fixxl/el-fueradoro/Manual/Bilder/rfm-dil-70x100.pdf

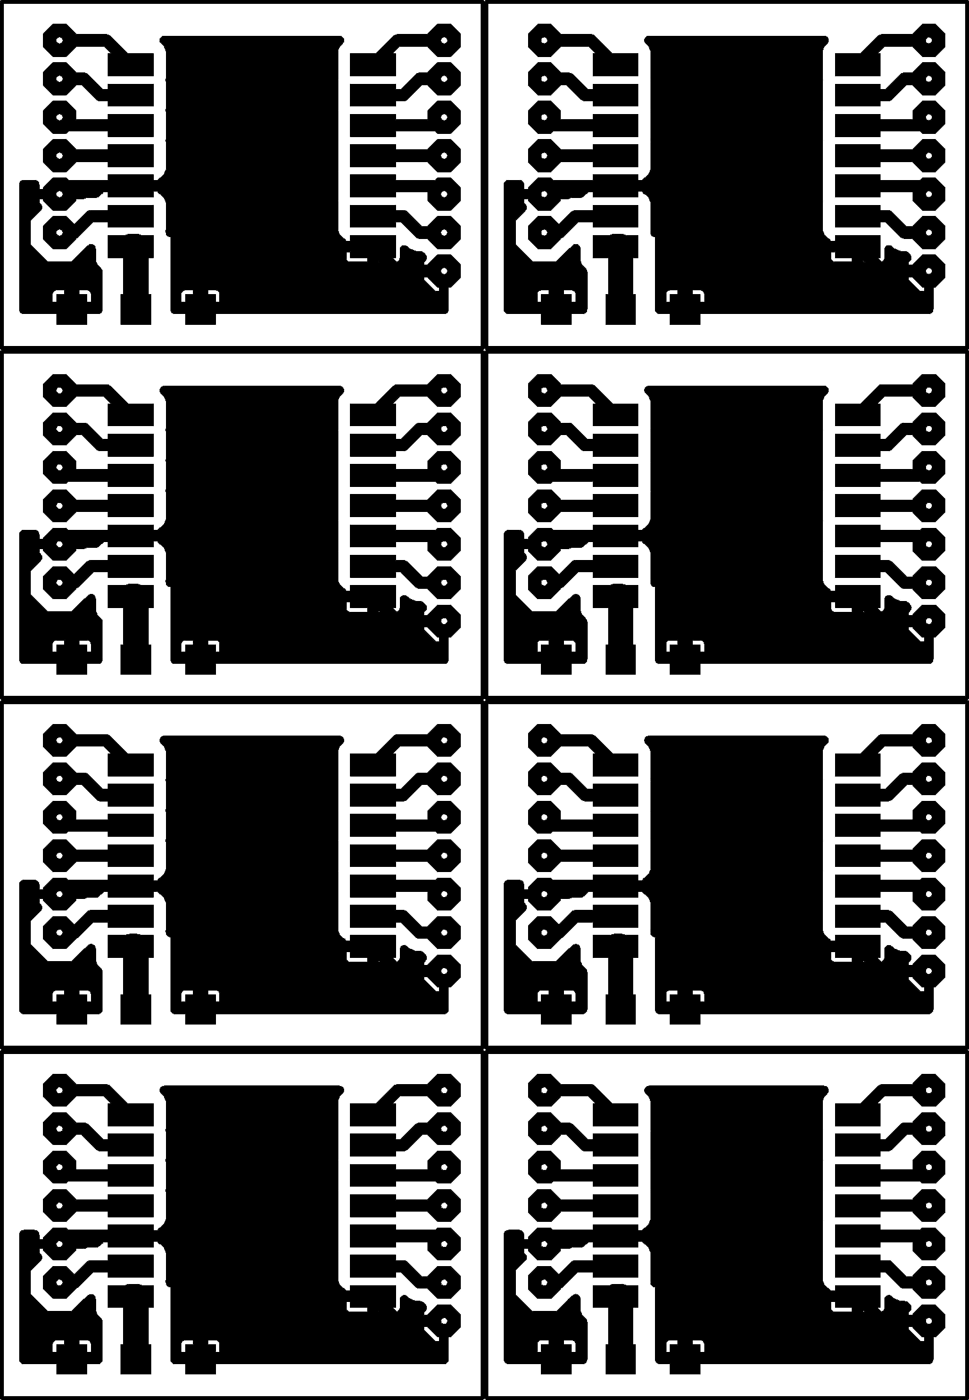
[picture p66: page 1]
