fixxl/el-fueradoro/Manual/Bilder/Transmitterschaltplan.pdf

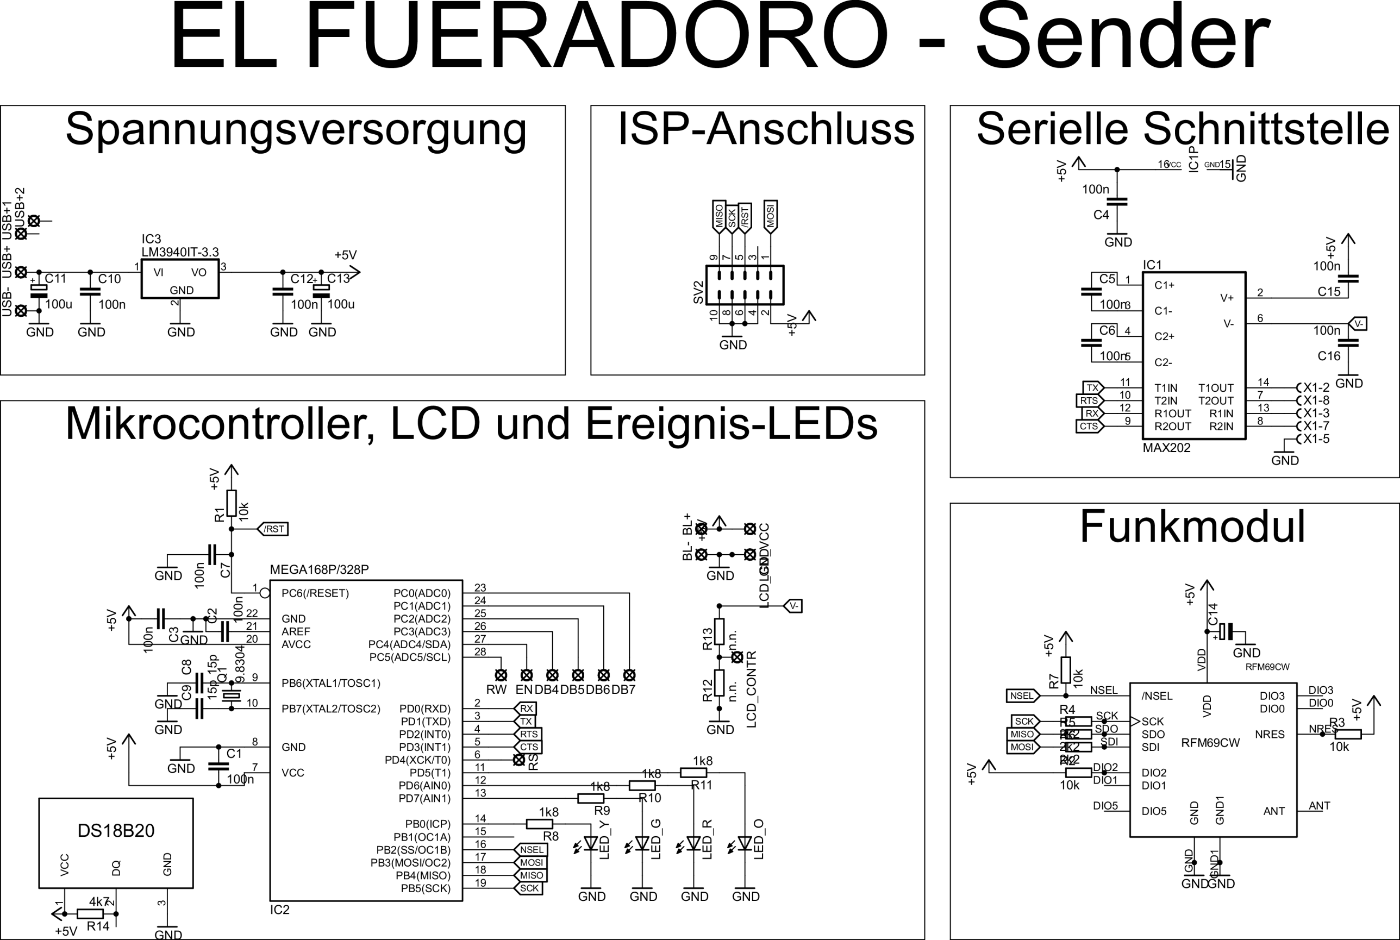
[picture p67: page 1]
