fixxl/el-fueradoro/Manual/Bilder/german.jpg

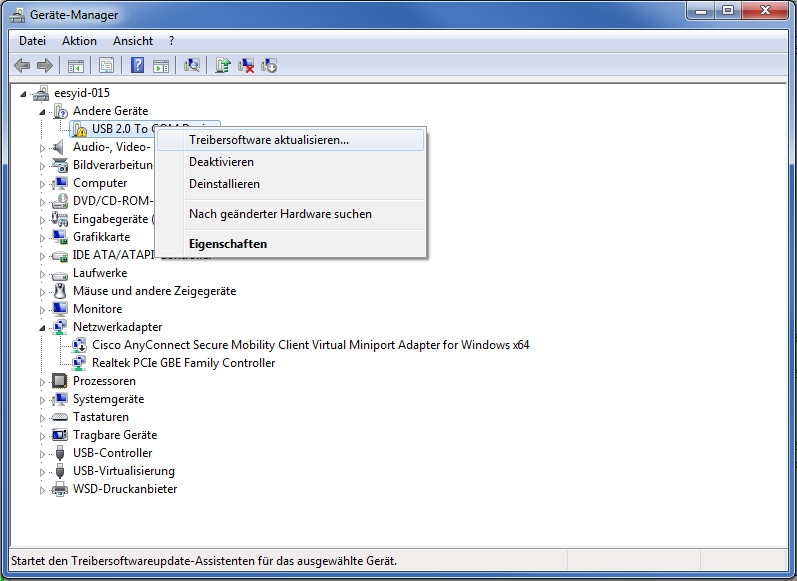
Manual/Bilder/german.jpg
