fixxl/el-fueradoro/Manual/Bilder/platine_v2.jpg

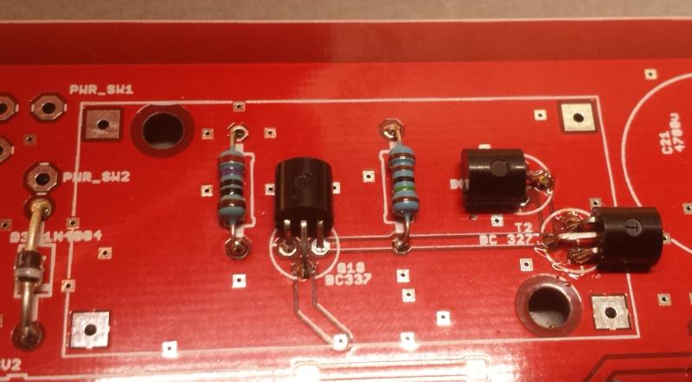
Manual/Bilder/platine_v2.jpg
