fixxl/el-fueradoro/Manual/Bilder/SenderMitAdapter.jpg

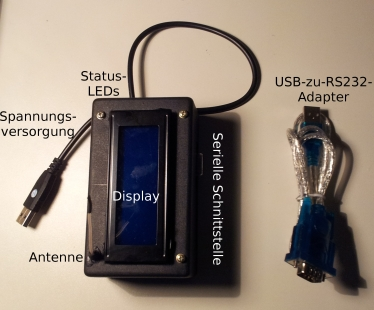
Manual/Bilder/SenderMitAdapter.jpg
