fixxl/el-fueradoro/Manual/Bilder/treiber.jpg

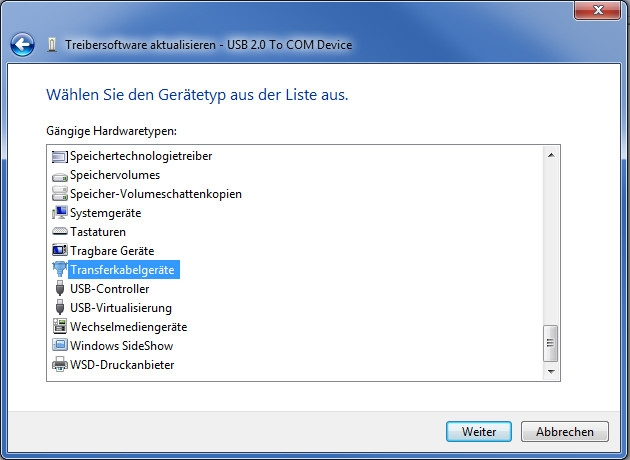
Manual/Bilder/treiber.jpg
