fixxl/el-fueradoro/Manual/Bilder/Zuendboxschaltplan.pdf

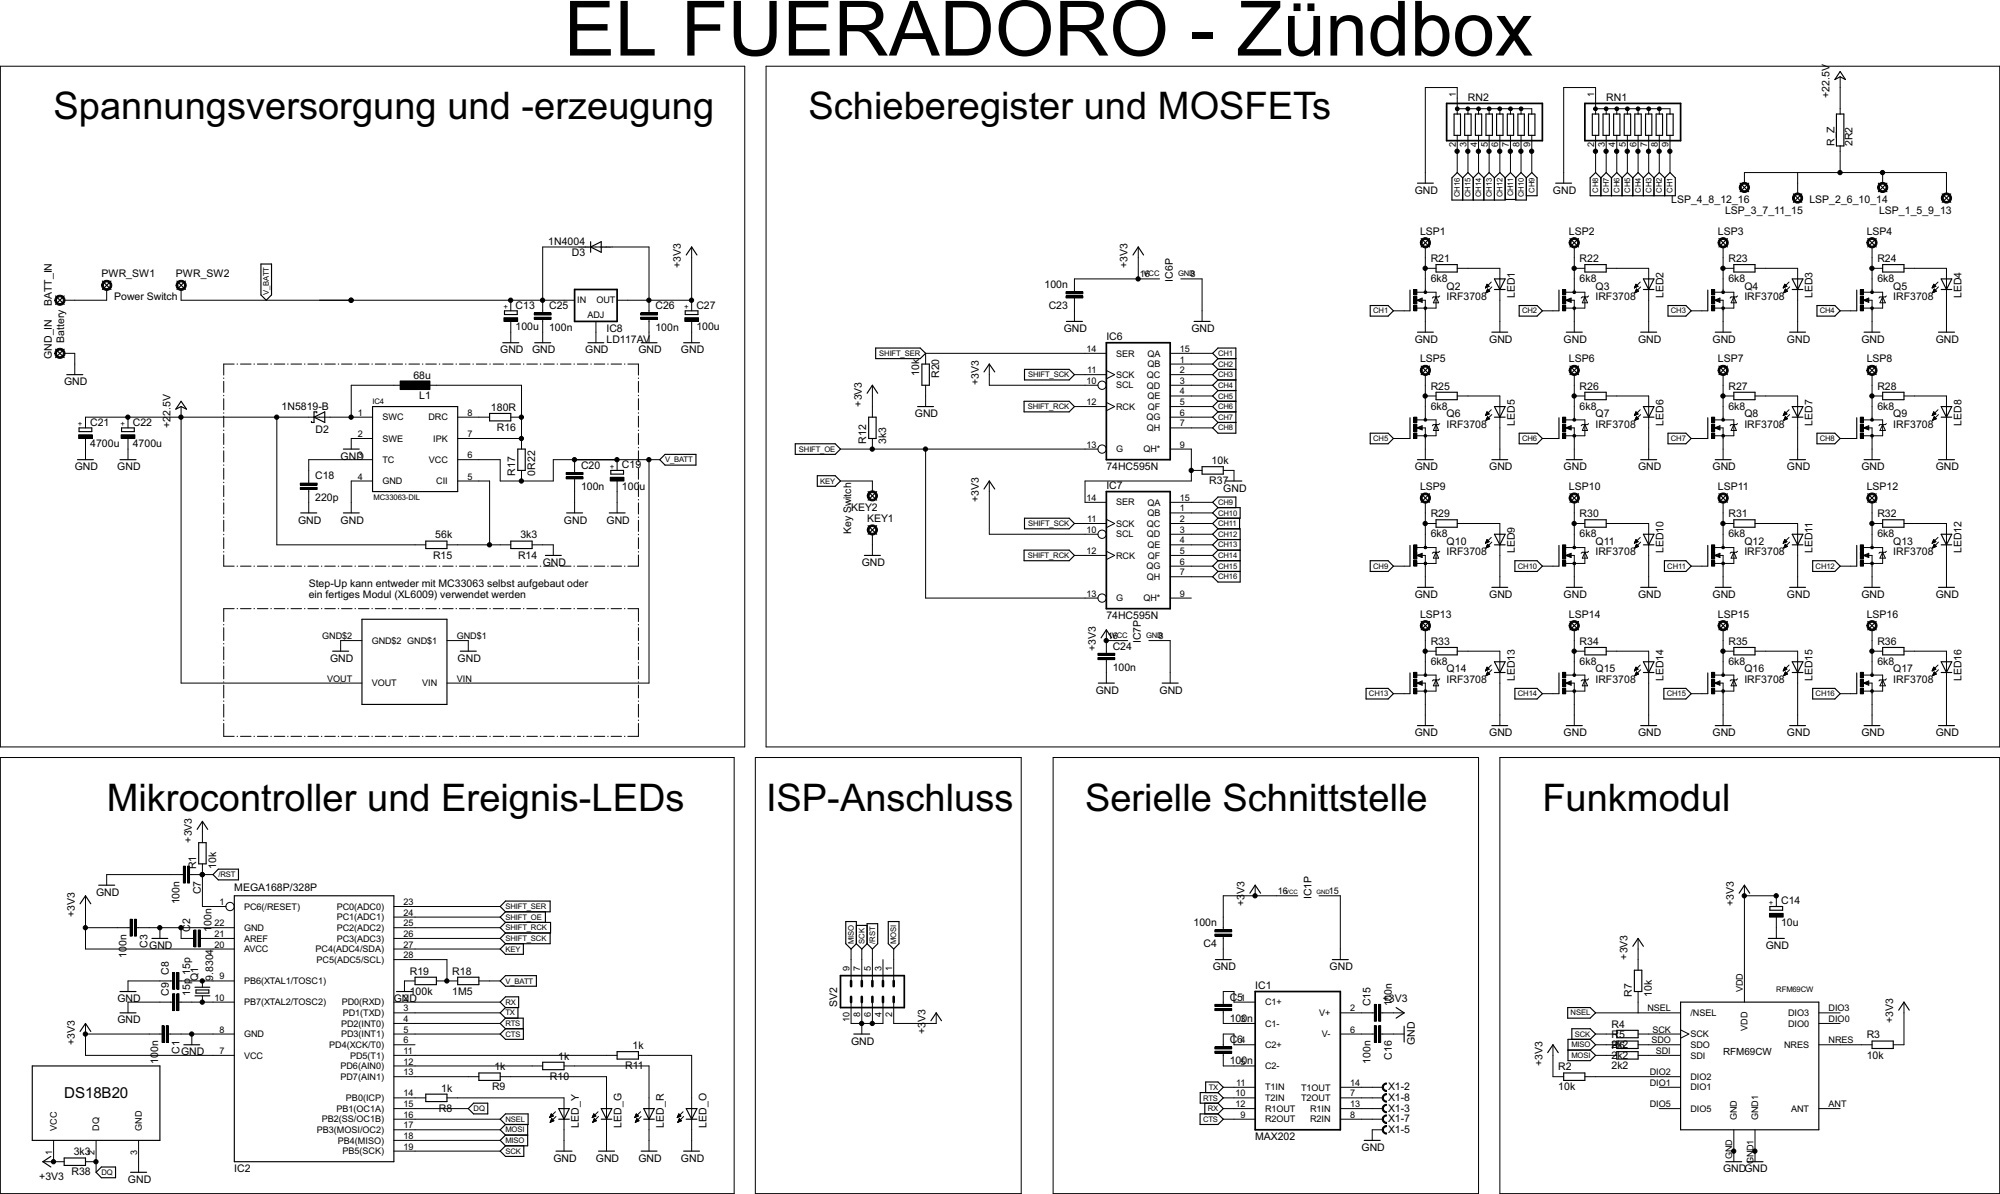
[picture p73: page 1]

Step-Up kann entweder mit MC33063 selbst aufgebaut oder
ein fertiges Modul (XL6009) verwendet werden

GND | AREF 21 AVCC 20 | SHIFT_RCK SHIFT_SCK

PB6(XTAL1/TOSC1) 9 | KEY
