fixxl/el-fueradoro/Manual/Bilder/Zuendboxbottom.pdf

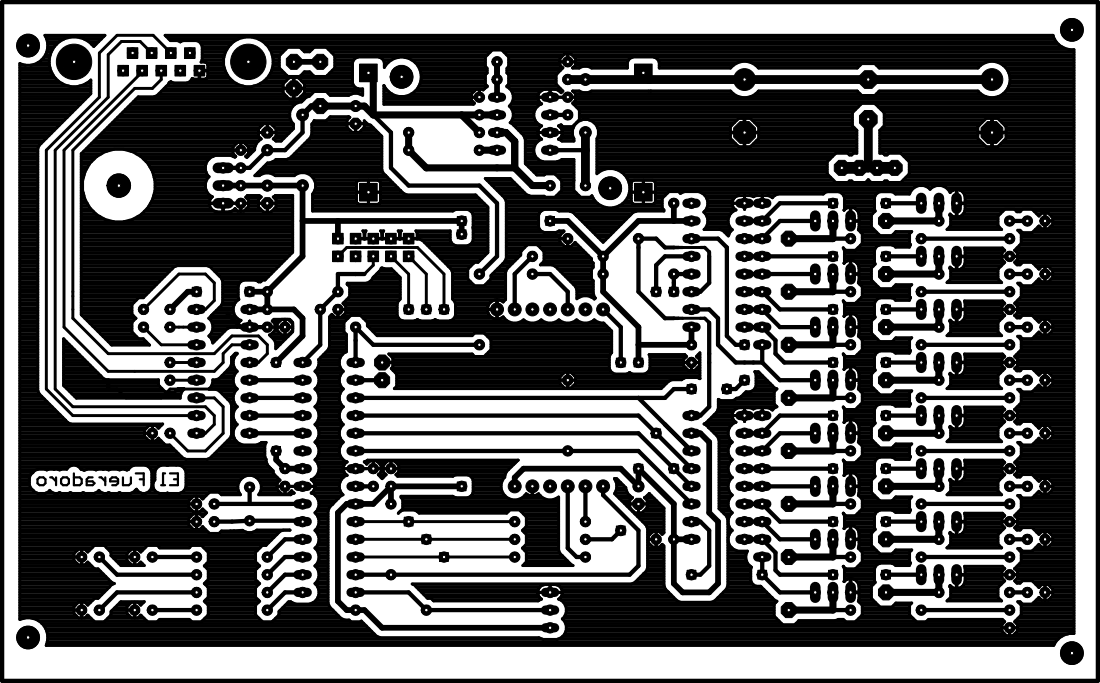
[picture p83: page 1]
