fixxl/el-fueradoro/Manual/Bilder/Zuendboxtop.pdf

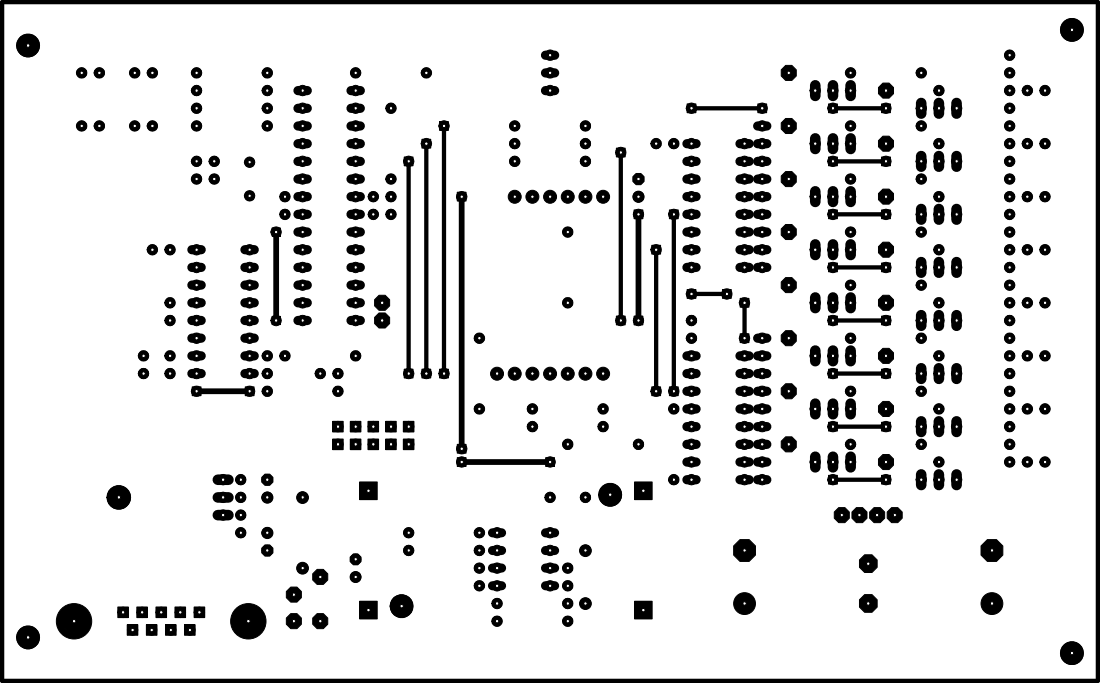
[picture p84: page 1]
