fixxl/el-fueradoro/Hexfiles/Updater/UpdateLoader.ini

[UpdateLoader]
ComPort=2
BootloaderPassword=Peda
FirmwareFilename=Pyro_v3_atmega328p_RFM69_HP.hex
Page=2

[Advanced]
BaudRate=9600
FirmwareKeyParseMode=1
ShowMemory=0
HideMessages=1
Enabled=1
ProgramWrite=1
ProgramVerify=1
ProgramStart=1
ReloadFile=1
DetectOneWire=0
ToggleDTR=0
InvertCom=0
EnableFirmwareKey=1
FirmwareKeyOnce=1
FirmwareKey=0A 6B 69 6C 6C 0A
ConnectTries=250

[PaketMode]
Enabled=1
MiniGUI=0
ModalGUI=0
HideAdvancedMode=1
LockFilename=0
LockPassword=1
HidePassword=1
