fixxl/el-fueradoro/Firmware_Minimodul/rfm69.h

/*
 * rfm69.h
 *
 * Definitionen und Funktionen zur Steuerung des Funkmoduls RFM69
 *
 */

#ifndef RFM69_H_
#define RFM69_H_

/* Carrierfrequenz in Hz */
#ifndef FREQUENCY
    #define FREQUENCY              869500000LL
#endif

/* Bitrate in bps (1200 ... 300000) and shall it be calculated as for RFM12
 * in order to get equal bitrate for RFM12 and RFM69 if used together? */
#define BITRATE                9600L
#define RFM12COMP              1

/* Minimum PA ramp up time in microseconds to set in register 0x12.
 * If value is not defined in table, next higher value will be chosen */
#define RFM_RAMP_UP            40

/* Output power in dBm (-18...13) */
#ifndef P_OUT_DBM
    #define P_OUT_DBM          10 // Output power in dBm
#endif

#ifndef HPVERSION
    #define HPVERSION          0
#endif

#ifndef SQUELCH_THRESHOLD
    #define SQUELCH_UPPER_LIMIT  -70
#endif

#ifndef RX_TIMEOUT_CTR_THRESHOLD_HIGH
    #define RX_TIMEOUT_CTR_THRESHOLD_HIGH 20
#endif

#ifndef RX_TIMEOUT_CTR_THRESHOLD_TP
    #define RX_TIMEOUT_CTR_THRESHOLD_TP 6
#endif

#ifndef RX_TIMEOUT_CTR_THRESHOLD_LOW
    #define RX_TIMEOUT_CTR_THRESHOLD_LOW 2
#endif
/* Pin assignment */
#define NSELPORT               C
#define NSEL                   3
#define SDIPORT                B
#define SDI                    3
#define SDOPORT                B
#define SDO                    4
#define SCKPORT                B
#define SCK                    5

/* Use Hardware-SPI if available? */
#define RFM69_USE_HARDWARE_SPI 1

// Don't change anything from here
#define XTALFREQ               32000000UL

#define NSEL_PORT              PORT( NSELPORT )
#define NSEL_DDR               DDR( NSELPORT )
#define NSEL_PIN               PIN( NSELPORT )
#define NSEL_NUMERIC           NUMPORT( NSELPORT )

#define SDI_PORT               PORT( SDIPORT )
#define SDI_DDR                DDR( SDIPORT )
#define SDI_PIN                PIN( SDIPORT )
#define SDI_NUMERIC            NUMPORT( SDIPORT )

#define SDO_PORT               PORT( SDOPORT )
#define SDO_DDR                DDR( SDOPORT )
#define SDO_PIN                PIN( SDOPORT )
#define SDO_NUMERIC            NUMPORT( SDOPORT )

#define SCK_PORT               PORT( SCKPORT )
#define SCK_DDR                DDR( SCKPORT )
#define SCK_PIN                PIN( SCKPORT )
#define SCK_NUMERIC            NUMPORT( SCKPORT )

#define ACTIVATE_RFM           NSEL_PORT &= ~( 1 << NSEL )
#define DEACTIVATE_RFM         NSEL_PORT |= ( 1 << NSEL )


#define FRF                    ( ( FREQUENCY * 524288LL + ( XTALFREQ / 2 ) ) / XTALFREQ )
#define FRF_MSB                ( ( FRF >> 16 ) & 0xFF )
#define FRF_MID                ( ( FRF >> 8 ) & 0xFF )
#define FRF_LSB                ( ( FRF ) & 0xFF )

#if RFM12COMP
    #define BR_VAL          \
        ( ( ( ( ( ( 344828L \
                    - ( BITRATE < 2694L ) * 301725L ) + ( BITRATE / 2 ) ) / BITRATE ) - 1 ) | ( ( BITRATE < 2694 ) * 0x80 ) ) )
 #if BR_VAL < 128
        #define BR             ( ( 10000000L + ( 29 * BR_VAL / 2 ) ) / ( 29 * ( BR_VAL + 1 ) ) )
 #else
        #define BR_VAL_S       ( ( BR_VAL - 127 ) * 8 )
        #define BR             ( ( 10000000L + ( 29 * BR_VAL_S / 2 ) ) / ( 29 * ( BR_VAL_S ) ) )
 #endif
#else
    #define BR                 BITRATE
#endif

#define DATARATE               ( ( XTALFREQ + ( BR / 2 ) ) / BR )
#define DATARATE_MSB           ( DATARATE >> 8 )
#define DATARATE_LSB           ( DATARATE & 0xFF )

#define P_OUT                  ((!HPVERSION && 1) * ( ( P_OUT_DBM + 18 + 0x80 ) * ( P_OUT_DBM > -19 ) * ( P_OUT_DBM < 14 )) + (HPVERSION && 1) * (( P_OUT_DBM + 11 + 0x60 ) * ( P_OUT_DBM > -12 ) * ( P_OUT_DBM < 21 ) ))

#ifndef MAX_COM_ARRAYSIZE
    #define MAX_COM_ARRAYSIZE      30
#endif

// Value for input timeout
#ifndef RFM69_TIMEOUTVAL
    #define RFM69_TIMEOUTVAL   ( F_CPU >> 1 )
#endif

#ifdef SPDR
    #define HASHARDSPI69       1
#else
    #define HASHARDSPI69       0
#endif


#define HARDWARE_SPI_69        (   RFM69_USE_HARDWARE_SPI && HASHARDSPI69 && ( SDO_NUMERIC == SDI_NUMERIC ) \
                               && ( SDO_NUMERIC == SCK_NUMERIC ) && ( SDO_NUMERIC == BPORT ) && ( SDI == 3 ) && ( SDO == 4 ) && ( SCK == 5 ) )

uint8_t rfm_cmd( uint16_t command, uint8_t wnr );   // Immediate access to register
uint8_t rfm_receiving( void );                      // Valid data received?
uint16_t rfm_status( void );                        // Contents of status registers 0x27 (15:8) and 0x28 (7:0)

uint8_t rfm_rxon( void );                           // Turn on Receiver
uint8_t rfm_rxoff( void );                          // Turn off Receiver
uint8_t rfm_txon( void );                           // Turn on Transmitter
uint8_t rfm_txoff( void );                          // Turn off Transmitter

uint8_t rfm_init( void );                           // Initialisation
void rfm_highpower( uint8_t enable );               // High Power Settings
uint8_t rfm_transmit( char *data, uint8_t length ); // Transmit data
uint8_t rfm_receive( char *data, uint8_t *length ); // Get received data
void rfm_setFrequency( char *farray );

uint8_t rfm_get_rssi_dbm( void );                   // Return RSSI-Value. Real RSSI = -1dBm * returned value

#endif
