fixxl/el-fueradoro/Firmware_Minimodul/rfm69.c

/*
 * rfm69.c
 *
 *  Created on: 15.06.2013
 *      Author: Felix
 */

#include "global.h"

#ifdef RFM69_H_

// SPI-Transfer
    static inline uint8_t rfm_spi( uint8_t spibyte ) {
        #if (HARDWARE_SPI_69)
            SPDR = spibyte;

            while ( !( SPSR & ( 1 << SPIF ) ) );

            spibyte = SPDR;
        #else
            for ( uint8_t i = 8; i; i-- ) {
                if ( spibyte & 0x80 ) {
                    SDI_PORT |= ( 1 << SDI );
                }
                else {
                    SDI_PORT &= ~( 1 << SDI );
                }

                spibyte <<= 1;
                SCK_PIN   = ( 1 << SCK ); // Fast-toggling SCK-Pin by writing to PIN-Register
                __asm__ __volatile__ ( "rjmp 1f\n 1:" );

                if ( SDO_PIN & ( 1 << SDO ) ) {
                    spibyte |= 0x01;
                }
                else {
                    spibyte &= 0xFE;
                }

                SCK_PIN = ( 1 << SCK );   // Fast-toggling SCK-Pin by writing to PIN-Register
            }
        #endif
        return spibyte;
    }

// Send 16-bit-command to RFM69 (1 bit write-/read-access, 7 bits register-number, 8 bits command)
    uint8_t rfm_cmd( uint16_t command, uint8_t wnr ) {
        // Split command in two bytes, merge with write-/read-flag
        uint8_t highbyte = ( wnr ? ( ( command >> 8 ) | 0x80 ) : ( ( command >> 8 ) & 0x7F ) );
        uint8_t lowbyte  = ( wnr ? ( command & 0x00FF ) : 0xFF );

        // Ensure correct idle levels, then enable module
        SCK_PORT &= ~( 1 << SCK );
        SDI_PORT &= ~( 1 << SDI );
        ACTIVATE_RFM;

        // SPI-Transfer
        rfm_spi( highbyte );
        lowbyte = rfm_spi( lowbyte );

        // Disable module
        DEACTIVATE_RFM;
        SDI_PORT &= ~( 1 << SDI );
        SCK_PORT &= ~( 1 << SCK );
        return lowbyte;
    }

    uint8_t rfm_receiving( void ) {
        /* This function returns
         * 0 if nothing was received
         * 1 if a packet has been received successfully
         * 2 if a timeout has occurred (no package detected after trigger)
         * 4 in case of a FIFO overflow
         */
        uint16_t status;
        status = rfm_status();

        // LSB of status must be 0 if module is plugged in
        if( !( status & ( 1 << 0 ) ) ) {
            // If payload not ready
            if( !( status & ( 1 << 2 ) ) ) {
                // No Payload and RSSI-Rx-Timeout -> Rx-Restart
                if ( status & ( 1 << 10 ) ) {
                    rfm_cmd( 0x2810, 1 );
                    rfm_cmd( ( rfm_cmd( 0x3DFF, 0 ) | 0x3D04 ), 1 );
                    return 2;
                }
                // FIFO overflow
                else if ( status & ( 1 << 4 ) ) {
                    rfm_cmd( 0x2810, 1 );
                    return 4;
                }
            }
            // Payload is ready
            else {
                return 1;
            }
        }
        return 0;
    }

    uint16_t rfm_status( void ) {
        uint16_t status = 0;
        ACTIVATE_RFM;
        rfm_spi ( 0x27 );
        status |= rfm_spi( 0x00 ) << 8;
        status |= rfm_spi( 0x00 );
        DEACTIVATE_RFM;
        return status;
    }

// ------------------------------------------------------------------------------------------------------------------------

    static uint8_t rfm_fifo_wnr( char *data, uint8_t wnr ) { // Address FIFO-Register in write- or read-mode
        ACTIVATE_RFM;

        // Write data bytes
        if ( wnr ) {
            // Make sure there's no array-overflow
            if ( data[0] > MAX_COM_ARRAYSIZE ) {
                data[0] = MAX_COM_ARRAYSIZE;
            }

            // Write-access register 0
            rfm_spi( 0x80 );

            // Transfer length
            rfm_spi( data[0] );

            // Transfer data
            for ( uint8_t i = 1; i <= data[0]; i++ ) {
                rfm_spi( data[i] );
            }
        }
        // Read data bytes
        else {
            // Read-access register 0
            rfm_spi( 0 );

            // Get length
            data[0] = rfm_spi( 0xFF );

            // Make sure there's no array-overflow
            if ( data[0] > MAX_COM_ARRAYSIZE ) {
                data[0] = MAX_COM_ARRAYSIZE;
            }

            // Get data
            for ( uint8_t i = 1; i <= data[0]; i++ ) {
                data[i] = rfm_spi( 0xFF );
            }
        }

        DEACTIVATE_RFM;
        return 0;
    }

    static inline void rfm_fifo_clear( void ) {
        rfm_cmd( 0x2810, 1 );
    }

// ------------------------------------------------------------------------------------------------------------------------

// Turn Transmitter on and off
    uint8_t rfm_txon( void ) {
        uint32_t utimer = RFM69_TIMEOUTVAL;
        rfm_highpower( 1 );
        rfm_cmd( 0x010C, 1 );                                          // TX on (set to transmitter mode in RegOpMode)

        while ( --utimer && !( rfm_cmd( 0x27FF, 0 ) & ( 1 << 7 ) ) );  // Wait for Mode-Ready- and TX-Ready-Flag

        return utimer ? 0 : 1;
    }

    uint8_t rfm_txoff( void ) {
        uint32_t utimer = RFM69_TIMEOUTVAL;
        rfm_cmd( 0x0104, 1 );                                          // TX off (set to standby mode in RegOpMode)

        while ( --utimer && !( rfm_cmd( 0x27FF, 0 ) & ( 1 << 7 ) ) );  // Wait for Mode-Ready-Flag

        return utimer ? 0 : 1;
    }

// Turn Receiver on and off
    uint8_t rfm_rxon( void ) {
        uint32_t utimer = RFM69_TIMEOUTVAL;
        rfm_highpower( 0 );
        rfm_cmd( ( rfm_cmd( 0x3DFF, 0 ) | 0x3D04 ), 1 );
        rfm_cmd( 0x0110, 1 );                                          // RX on (set to receiver mode in RegOpMode)

        while ( --utimer && !( rfm_cmd( 0x27FF, 0 ) & ( 1 << 7 ) ) );  // Wait for Mode-Ready--Flag

        return utimer ? 0 : 1;
    }

    uint8_t rfm_rxoff( void ) {
        uint32_t utimer = RFM69_TIMEOUTVAL;
        rfm_cmd( 0x0104, 1 );                                          // RX off (set to standby mode in RegOpMode)

        while ( --utimer && !( rfm_cmd( 0x27FF, 0 ) & ( 1 << 7 ) ) );  // Wait for Mode-Ready-Flag

        return utimer ? 0 : 1;
    }

// Get RSSI-Value
    uint8_t rfm_get_rssi_dbm( void ) {
        uint32_t utimer = RFM69_TIMEOUTVAL;

        if ( !rfm_cmd( 0x6FFF, 0 ) ) {
            rfm_cmd( 0x2301, 1 );

            while ( --utimer && !( rfm_cmd( 0x23FF, 0 ) & ( 1 << 1 ) ) );
        }

        return rfm_cmd( 0x24FF, 0 ) >> 1;
    }

// ------------------------------------------------------------------------------------------------------------------------

// Bitrate config according to RFM12-recommendations (orthogonal frequencies)
    static inline void rfm_setbit( uint32_t bitrate ) {
        uint8_t  bw, afc_bw, logemu;
        uint16_t freqdev;

        uint32_t mant, expo, myfreq = FREQUENCY;

        // freqdev = bitrate => beta = 2
        freqdev = ( 512ULL * bitrate + 15625 ) / 31250;

        // RX-Bandwidth
        // Start with minimum bandwidth setting
        mant = 24;
        expo = 1 << 7;

        // Increase bandwidth until it's at least FDEV + Bitrate/2 with FDEV = Bitrate
        while ( ( 3 * bitrate / 2 > ( 32000000 / ( mant * 4 * expo ) ) ) && ( mant + expo > 17) ) {
            mant -= 4;

            if ( mant < 16 ) {
                if ( expo > 1 ) {
                    expo >>= 1;
                    mant   = 24;
                }
                else {
                    mant = 16;
                }
            }
        }

        // Loop-implementation of log2
        logemu = 0;
        expo >>= 1;
        while ( expo ) {
            expo >>= 1;
            logemu++;
        }

        bw = ( ( ( mant - 16 ) / 4 ) << 3 ) | logemu;

        // AFC-Bandwidth
        uint32_t xtalTol = ( 1ULL * myfreq + 50000UL ) / 100000ULL; // 10 ppm of RF frequency

        // Start with minimum bandwidth setting
        mant = 24;
        expo = 1 << 7;

        // Increase bandwidth until it's at least FDEV + Bitrate/2 + Tolerance with FDEV = Bitrate
        while ( ( 3 * bitrate / 2 + xtalTol > ( 32000000 / ( mant * 4 * expo ) ) ) && ( mant + expo > 17) ) {
            mant -= 4;

            if ( mant < 16 ) {
                if ( expo > 1 ) {
                    expo >>= 1;
                    mant   = 24;
                }
                else {
                    mant = 16;
                }
            }
        }

        // Loop-implementation of log2
        logemu = 0;
        expo >>= 1;
        while ( expo ) {
            expo >>= 1;
            logemu++;
        }

        afc_bw = ( ( ( mant - 16 ) / 4 ) << 3 ) | logemu;

        // Frequency Deviation
        rfm_cmd( 0x0500 | ( freqdev >> 8 ), 1 );
        rfm_cmd( 0x0600 | ( freqdev & 0xFF ), 1 );
        // Data Rate
        rfm_cmd( 0x0300 | DATARATE_MSB, 1 );
        rfm_cmd( 0x0400 | DATARATE_LSB, 1 );
        // Receiver Bandwidth
        rfm_cmd( 0x1940 | bw, 1 );
        // AFC-BW
        rfm_cmd( 0x1A40 | afc_bw, 1 );
    }

// Initialise RFM
    uint8_t rfm_init( void ) {
        uint32_t utimer;
        uint8_t  timeoutval;

        // Ramp-up look up table
        static const uint16_t rfm_ramp_up_table[ 16 ] = { 3400, 2000, 1000, 500, 250, 125, 100, 62, 50, 40, 31, 25, 20, 15, 12, 10 };

        // Configure SPI inputs and outputs
        NSEL_PORT |= ( 1 << NSEL );
        SDO_PORT  |= ( 1 << SDO );
        SDO_DDR   &= ~( 1 << SDO );
        SDI_DDR   |= ( 1 << SDI );
        SCK_DDR   |= ( 1 << SCK );
        NSEL_DDR  |= ( 1 << NSEL );
        #ifdef SPCR
            #if HARDWARE_SPI_69

                // Activate and configure hardware SPI at F_CPU/16
                if ( !( SPCR & ( 1 << SPE ) ) ) {
                    SPCR |= ( 1 << SPE | 1 << MSTR | 1 << SPR0 );
                }

            #endif
        #endif

        uint8_t rfm_fail = ( rfm_cmd( 0x10FF, 0 ) != 0x24 ) && 1;

        for ( uint8_t i = 3; i; i-- ) {
            _delay_ms( 4 );
            rfm_cmd( 0x0202, 1 );                                                                                        // FSK, Packet mode, BT=.5
            // Bitrate + corresponding settings (Receiver bandwidth, frequency deviation)
            rfm_setbit( BR );
            // DIO-Mapping
            rfm_cmd( 0x2540, 1 );                                                                                        // Clkout, FifoFull, FifoNotEmpty,
                                                                                                                         // FifoLevel, PacketSent/CrcOk
            rfm_cmd( 0x26A7, 1 );                                                                                        // Clock-Out off
            // Carrier frequency
            rfm_cmd( 0x0700 | FRF_MSB, 1 );
            rfm_cmd( 0x0800 | FRF_MID, 1 );
            rfm_cmd( 0x0900 | FRF_LSB, 1 );
            // Packet config
            rfm_cmd( 0x3790, 1 );                                                                                        // Variable length, No DC-free
                                                                                                                         // encoding/decoding, CRC-Check, No
                                                                                                                         // Address filter
            rfm_cmd( 0x3800 + MAX_COM_ARRAYSIZE, 1 );                                                                    // Max. Payload-Length
            rfm_cmd( 0x3C80, 1 );                                                                                        // Tx-Start-Condition: FIFO not empty
            rfm_cmd( 0x3D30, 1 );                                                                                        // Packet-Config2
            // Preamble length 4 bytes
            rfm_cmd( 0x2C00, 1 );
            rfm_cmd( 0x2D04, 1 );
            // Sync-Mode
            rfm_cmd( 0x2E88, 1 );                                                                                        // set FIFO mode
            rfm_cmd( 0x2F2D, 1 );                                                                                        // sync word MSB to 0x2D
            rfm_cmd( 0x30D4, 1 );                                                                                        // sync word LSB to 0xD4
            // Receiver config
            rfm_cmd( 0x1800, 1 );                                                                                        // LNA: 50 Ohm Input Impedance,
                                                                                                                         // Automatic
                                                                                                                         // Gain Control
            rfm_cmd( 0x582D, 1 );                                                                                        // High sensitivity mode
            rfm_cmd( 0x6F30, 1 );                                                                                        // Improved DAGC (for normal beta, beta
                                                                                                                         // = 2 -> beta >= 2
            rfm_cmd( 0x29CF, 1 );                                                                                        // RSSI mind. -103.5 dBm
            rfm_cmd( 0x1E2D, 1 );                                                                                        // AFC auto on and clear
            rfm_cmd( 0x2A00, 1 );                                                                                        // No Timeout after Rx-Start if no
                                                                                                                         // RSSI-Interrupt occurs

            uint8_t ramp_index = 15;
            while ( ramp_index && ( rfm_ramp_up_table[ ramp_index ] < RFM_RAMP_UP ) )
                ramp_index--;
            rfm_cmd( 0x1200 | ( ramp_index & 0x0F ), 1 );                                                                // No Timeout after Rx-Start if no RSSI
                                                                                                                         // interrupt occurs

            timeoutval = RFM_SHORT_LENGTH + rfm_cmd( 0x2DFF, 0 ) + ( ( ( rfm_cmd( 0x2EFF, 0 ) & 0x38 ) >> 3 ) + 1 ) + 4; // Max. Arraysize + Preamble length +
                                                                                                                         // Sync Word length + CRC + Length + 1
                                                                                                                         // Byte Spare

            rfm_cmd( 0x2B00 | ( timeoutval >> 1 ), 1 );                                                                  // Timeout after RSSI-Interrupt if no
                                                                                                                         // Payload-Ready-Interrupt occurs

            rfm_cmd( 0x131B, 1 );                                                                                        // OCP to 100 mA (changes with High
                                                                                                                         // Power)

            rfm_cmd( 0x1100 | P_OUT, 1 );                                                                                // Set Output Power
        }

        rfm_cmd( 0x0A80, 1 );                                          // Start RC-Oscillator
        utimer = RFM69_TIMEOUTVAL;

        while ( --utimer && !( rfm_cmd( 0x0A00, 0 ) & ( 1 << 6 ) ) );  // Wait for RC-Oscillator

        rfm_rxon();

        return rfm_fail;
    }

    void rfm_highpower( uint8_t enable ) {
        if ( enable && ( P_OUT_DBM > 5 ) && HPVERSION ) {
            rfm_cmd( 0x130F, 1 );
            rfm_cmd( 0x5A5D, 1 );
            rfm_cmd( 0x5C7C, 1 );
        }
        else {
            rfm_cmd( 0x131B, 1 );
            rfm_cmd( 0x5A55, 1 );
            rfm_cmd( 0x5C70, 1 );
        }
    }

// Transmit data stream
    uint8_t rfm_transmit( char *data, uint8_t length ) {
        char fifoarray[MAX_COM_ARRAYSIZE + 1];

        // Turn off receiver, switch to Standby
        rfm_rxoff();
        // Clear FIFO
        rfm_fifo_clear();

        // Limit length
        if ( length > MAX_COM_ARRAYSIZE - 1 ) {
            length = MAX_COM_ARRAYSIZE - 1;
        }

        // Write data to FIFO-array
        fifoarray[0] = length; // Number of data bytes

        for ( uint8_t i = 0; i < length; i++ ) { // Data bytes
            fifoarray[1 + i] = data[i];
        }

        fifoarray[length + 1] = '\0'; // Terminate string
        // Write data to FIFO
        rfm_fifo_wnr( fifoarray, 1 );
        // Turn on transmitter (Transmitting starts automatically if FIFO not empty)
        rfm_txon();

        // Wait for Package Sent (150 Byte-Times)
        uint32_t utimer = ( ( 75ULL * F_CPU + BR * 8 ) / ( 16 * BR ) );
        uint8_t  regval = 0;

        while ( utimer-- && !regval ) {
            regval = rfm_cmd( 0x2800, 0 ) & 0x09; // Check for package sent and module plugged in
		}

        rfm_txoff();
        return ( !utimer || ( regval & 0x01 ) ); // 0 : successful, 1 : error
    }

// Receive data stream
    uint8_t rfm_receive( char *data, uint8_t *length ) {
        char    fifoarray[MAX_COM_ARRAYSIZE + 1];
        uint8_t length_local;

        // Turn off receiver, switch to Standby
        rfm_rxoff();

        // Read FIFO-data into FIFO-array
        rfm_fifo_wnr( fifoarray, 0 );

        // Read data from FIFO-array
        length_local = fifoarray[0];             // Number of data bytes

        if ( length_local > MAX_COM_ARRAYSIZE - 1 ) {
            length_local = MAX_COM_ARRAYSIZE - 1; // Limit length
        }

        for ( uint8_t i = 0; i < length_local; i++ ) {
            data[i] = fifoarray[i + 1];           // Data bytes
        }

        data[length_local] = '\0'; // Terminate string

        // Clear FIFO after readout (not necessary, FIFO is cleared anyway when switching from STANDBY to RX)
        rfm_fifo_clear();

        // Write local variable to pointer
        *length = length_local;

        // Return value is for compatibility reasons with RFM12
        // It's always 0 because PayloadReady only occurs after successful hardware CRC
        return 0;                  // 0 : successful, 1 : error
    }

    void rfm_setFrequency( char *farray ) {
        rfm_rxoff();

        // Carrier frequency
        rfm_cmd( 0x0700 | farray[0], 1 );
        rfm_cmd( 0x0800 | farray[1], 1 );
        rfm_cmd( 0x0900 | farray[2], 1 );

        rfm_rxon();
    }
#endif
