fixxl/el-fueradoro/Firmware_Zuendbox_v3/dm13a.c

/*
 * dm13a.c
 *
 *  Created on: 15.06.2013
 *      Author: Felix
 */

#include "global.h"

// Initialize
void dm_init( void ) {
    // Activate pullup at /EN, so /EN stays high when switching from input to output
    // and outputs of the 74HC595 stay in high-Z-mode!
    EN_PORT |= ( 1 << EN );

    // Configure pins as outputs
    DAI_DDR |= 1 << DAI;
    EN_DDR  |= 1 << EN;
    LAT_DDR |= 1 << LAT;
    DCK_DDR |= 1 << DCK;

    // All outputs except /EN to low
    DAI_PORT &= ~( 1 << DAI );
    LAT_PORT &= ~( 1 << LAT );
    DCK_PORT &= ~( 1 << DCK );

    // Set shift-register values to 0...
    for ( uint8_t j = 3; j; j-- ) {
        for ( uint8_t i = ( DM_CHANNELS + 4 ); i; i-- ) {
            DCK_PIN = ( 1 << DCK ); // Pin high after toggling
            DCK_PIN = ( 1 << DCK ); // Pin low after toggling
        }

        // ... and apply shift-register to output register.
        LAT_PIN = ( 1 << LAT ); // Pin high after toggling
        LAT_PIN = ( 1 << LAT ); // Pin low after toggling
    }

    _delay_ms( 1 );

    // Now outputs are all low and can be activated!
    EN_PORT &= ~( 1 << EN );

    #if HARDWARE_SPI_DM

        // Activate and configure hardware SPI at F_CPU/16
        if ( !( SPCR & ( 1 << SPE ) ) ) {
            SPCR |= ( 1 << SPE | 1 << MSTR | 1 << SPR0 );
        }

    #endif
}

void dm_enable( void ) {
    EN_PORT &= ~( 1 << EN );
}

void dm_disable( void ) {
    EN_PORT |= ( 1 << EN );
}

// Transfer 16 bit pattern to outputs
void dm_shiftout( uint32_t scheme ) {
    DAI_PORT &= ~( 1 << DAI );
    DCK_PORT &= ~( 1 << DCK );
    LAT_PORT &= ~( 1 << LAT );
    uint32_t mask;

    #if HARDWARE_SPI_DM
        mask = 255UL << ((( DM_CHANNELS-1*(DM_CHANNELS>0) ) / 8 ) * 8);                // Shift 0xFF to the 0th, 8th, 16th or 24th bit, depending on number of channels
        for(uint8_t i = ((DM_CHANNELS + 7) / 8); i; i--) {                             // Run the loop at least once or up to four times depending on number of channels
            SPDR = (scheme & mask) >> ((( DM_CHANNELS-1*(DM_CHANNELS>0) ) / 8 ) * 8);  // Shift current 8 bit word to bits 7:0 and write to SPI-Data register
            scheme <<= 8;
            while ( !( SPSR & ( 1 << SPIF ) ) );
        }

    #else
        mask = 1UL << ( DM_CHANNELS - 1 );

        for ( uint8_t i = DM_CHANNELS; i; i-- ) {
            if ( scheme & mask ) {
                DAI_PORT |= 1 << DAI;
            }

            DCK_PIN   = ( 1 << DCK ); // Pin high after toggling
            DCK_PIN   = ( 1 << DCK ); // Pin low after toggling
            DAI_PORT &= ~( 1 << DAI );
            mask    >>= 1;
        }
    #endif
    LAT_PIN = ( 1 << LAT ); // Pin high after toggling
    LAT_PIN = ( 1 << LAT ); // Pin low after toggling
}
